tonykoop/didgeridoo/images/2022-03-19 16.24.06.jpg

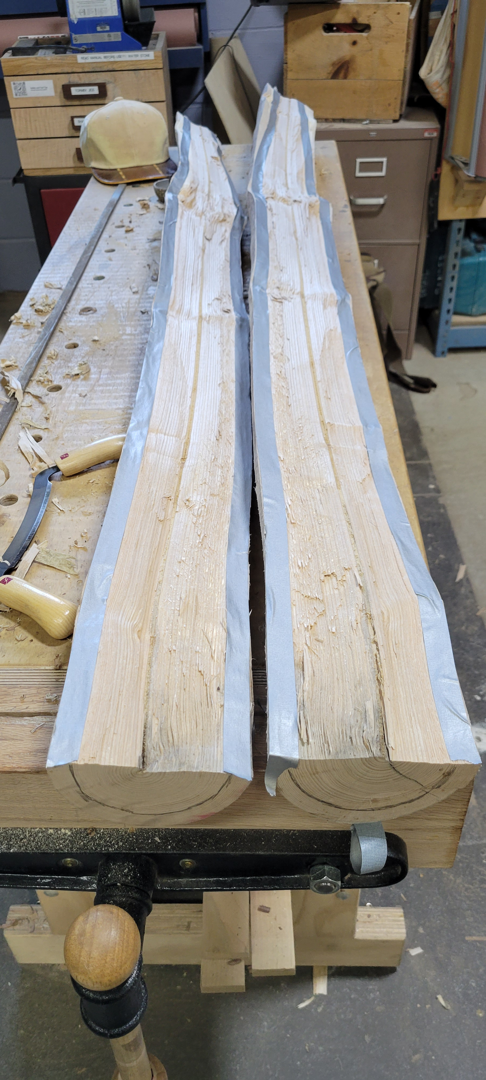
images/2022-03-19 16.24.06.jpg
