tonykoop/didgeridoo/images/IMG_20220212_210026_503.jpg

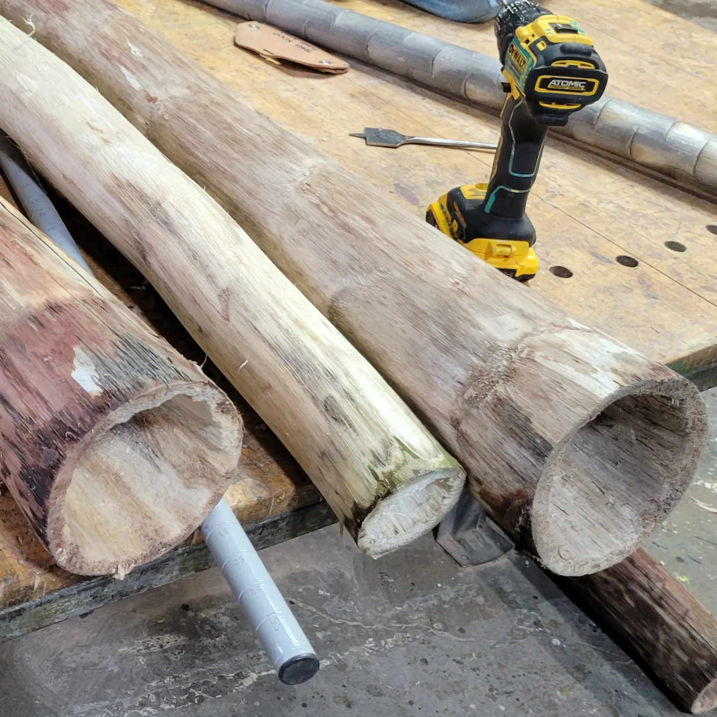
images/IMG_20220212_210026_503.jpg
