tonykoop/didgeridoo/images/macro/stave-seam-bell-flare.png

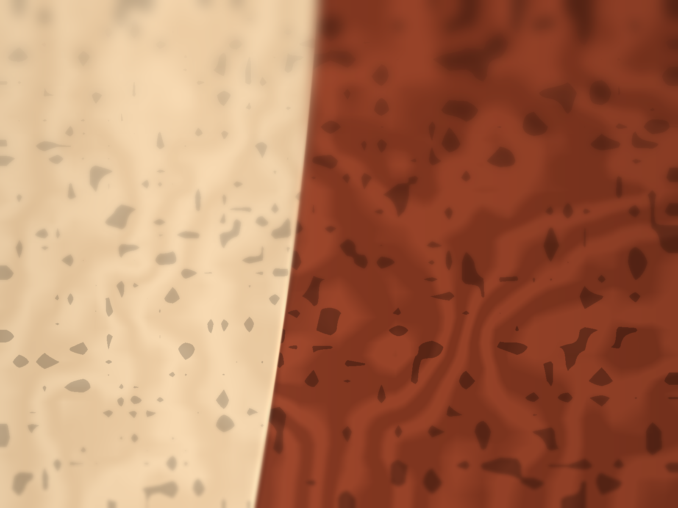
images/macro/stave-seam-bell-flare.png
